mediumrehr/oxvox/Firmware/oxvox/tables.h

#ifndef _TABLES_H_
#define _TABLES_H_

#ifdef _50KHZ_
	static nrf_pwm_values_common_t SinTableC_50k[191] = {
		0,
		0,
		0,
		1,
		1,
		2,
		2,
		3,
		4,
		5,
		6,
		8,
		9,
		11,
		13,
		15,
		17,
		19,
		21,
		23,
		26,
		28,
		31,
		34,
		37,
		40,
		43,
		46,
		49,
		53,
		56,
		60,
		63,
		67,
		71,
		74,
		78,
		82,
		86,
		90,
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
	};

	static nrf_pwm_values_common_t SinTableD_50k[170] = {
		0,
		0,
		0,
		1,
		1,
		2,
		3,
		4,
		5,
		6,
		8,
		10,
		11,
		13,
		16,
		18,
		20,
		23,
		26,
		29,
		32,
		35,
		38,
		42,
		45,
		49,
		52,
		56,
		60,
		64,
		68,
		73,
		77,
		81,
		86,
		90,
		95,
		99,
		104,
		108,
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
	};

	static nrf_pwm_values_common_t SinTableE_50k[152] = {
		0,
		0,
		0,
		1,
		2,
		3,
		4,
		5,
		7,
		9,
		11,
		13,
		15,
		18,
		21,
		24,
		27,
		30,
		33,
		37,
		41,
		45,
		49,
		53,
		57,
		62,
		66,
		71,
		76,
		81,
		86,
		91,
		96,
		101,
		106,
		111,
		116,
		122,
		127,
		132,
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
	};

	static nrf_pwm_values_common_t SinTableF_50k[143] = {
		0,
		0,
		0,
		1,
		2,
		3,
		4,
		6,
		7,
		9,
		12,
		14,
		17,
		20,
		23,
		26,
		29,
		33,
		37,
		41,
		45,
		49,
		54,
		58,
		63,
		68,
		73,
		78,
		83,
		89,
		94,
		99,
		105,
		110,
		116,
		121,
		127,
		133,
		138,
		144,
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
	};

	static nrf_pwm_values_common_t SinTableG_50k[128] = {
		0,
		0,
		1,
		1,
		2,
		4,
		5,
		7,
		9,
		12,
		15,
		18,
		21,
		25,
		29,
		33,
		37,
		41,
		46,
		51,
		56,
		62,
		67,
		73,
		78,
		84,
		90,
		96,
		102,
		108,
		115,
		121,
		127,
		133,
		139,
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
		0,
		2,
		8,
		17,
		30,
		45,
		64,
		84,
		105,
		127,
		149,
		170,
		191,
		209,
		224,
		237,
		246,
		252,
		254,
		252,
		246,
		237,
		224,
		209,
		191,
		170,
		149,
		127,
		105,
		84,
		64,
		45,
		30,
		17,
		8,
		2
	};
#endif // 50kHz/20kHz

#endif // _TABLES_H_
