mediumrehr/oxvox/Firmware/oxvox/screens.h

#ifndef _SCREENS_H_
#define _SCREENS_H_

static uint8_t buffer[SSD1306_LCDHEIGHT * SSD1306_LCDWIDTH / 8] = {
		0x00, 0x00, 0x00, 0x00, 0x00, 0x00, 0x00, 0x00, 0x00, 0x00, 0x00, 0x00, 0x00, 0x00, 0x00, 0x00, 
		0x00, 0x00, 0x00, 0x00, 0x00, 0x00, 0x00, 0x00, 0x00, 0x00, 0x00, 0x00, 0x00, 0x00, 0x00, 0x00, 
		0x00, 0x00, 0x00, 0x00, 0x00, 0x00, 0x00, 0x00, 0x00, 0x00, 0x00, 0x00, 0x00, 0x00, 0x00, 0x00, 
		0x00, 0x00, 0x00, 0x00, 0x00, 0x00, 0x00, 0x00, 0x00, 0x00, 0x00, 0x00, 0x00, 0x00, 0x00, 0x00, 
		0x00, 0x00, 0x00, 0x00, 0x00, 0x00, 0x80, 0x00, 0x80, 0x00, 0x80, 0x00, 0x80, 0x00, 0x00, 0x00, 
		0x00, 0x00, 0x00, 0x00, 0x00, 0x00, 0x00, 0x00, 0x80, 0x00, 0x80, 0x00, 0x00, 0x00, 0x00, 0x00, 
		0x00, 0x00, 0x00, 0x00, 0x00, 0x00, 0x00, 0x00, 0x00, 0x00, 0x00, 0x00, 0x00, 0x00, 0x00, 0x00, 
		0x00, 0x00, 0x00, 0x00, 0x00, 0x00, 0x00, 0x00, 0x00, 0x00, 0x00, 0x00, 0x00, 0x00, 0x00, 0x00, 
		0x28, 0x14, 0x28, 0x14, 0x0a, 0x14, 0x0a, 0x14, 0x0a, 0x14, 0x0a, 0x14, 0x0a, 0x05, 0x0a, 0x05, 
		0x0a, 0x05, 0x0a, 0x04, 0x0a, 0x14, 0x0a, 0x14, 0x2a, 0x14, 0x28, 0x14, 0x28, 0x14, 0x08, 0x14, 
		0x0a, 0x14, 0x0a, 0x14, 0x0a, 0x14, 0x0a, 0x04, 0x0a, 0x04, 0x0a, 0x04, 0x0a, 0x05, 0x0a, 0x05, 
		0x0a, 0x04, 0x0a, 0x04, 0x0a, 0x04, 0x0a, 0x14, 0x08, 0x14, 0x28, 0x14, 0x28, 0x14, 0x08, 0x14, 
		0x08, 0x04, 0x0a, 0x04, 0x0a, 0x05, 0x0a, 0x05, 0x02, 0x05, 0x02, 0x05, 0x02, 0x05, 0x02, 0x05, 
		0x02, 0x05, 0x0a, 0x05, 0x0a, 0x05, 0x02, 0x05, 0x02, 0x05, 0x02, 0x05, 0x02, 0x05, 0x0a, 0x04, 
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
		0x00, 0x00, 0x00, 0x00, 0x00, 0x00, 0x00, 0x00, 0x00, 0x00, 0x00, 0x00, 0x00, 0x00, 0x00, 0x00, 
		0x00, 0x00, 0x00, 0x00, 0x00, 0x00, 0x00, 0xff, 0x00, 0x55, 0xaa, 0x55, 0xaa, 0x55, 0xaa, 0x55, 
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
};

#endif // _SCREENS_H_
